Talandar99/rpi_zero_ebook_reader/images/waveshare_eink_display.png

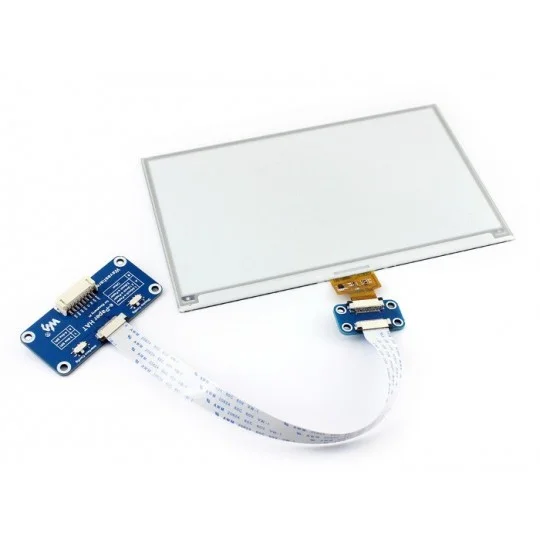
images/waveshare_eink_display.png
